dczia/theremini/documentation/gerber.png_Combined_Bottom.png

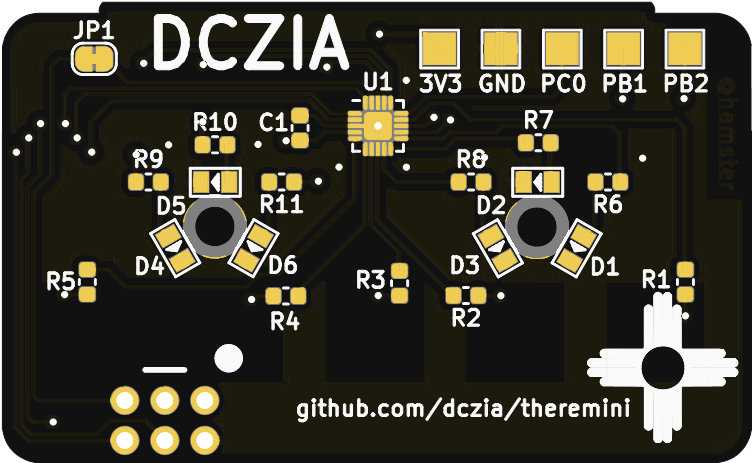
documentation/gerber.png_Combined_Bottom.png
