dczia/theremini/documentation/gerber.png_Combined_Top.png

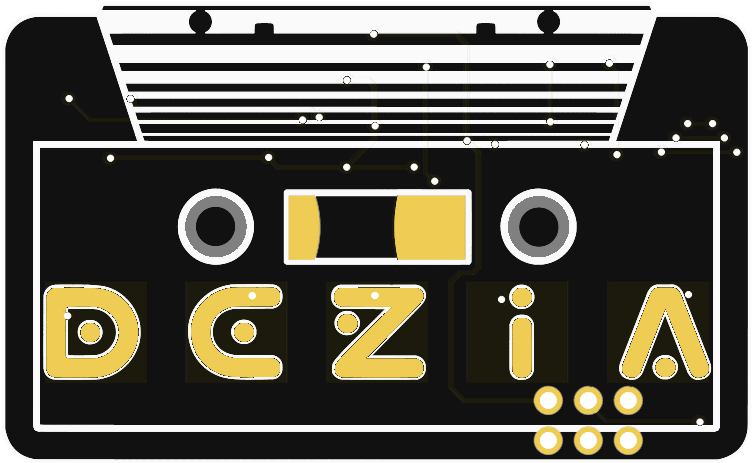
documentation/gerber.png_Combined_Top.png
