dczia/theremini/documentation/panel.png_Combined_Bottom.png

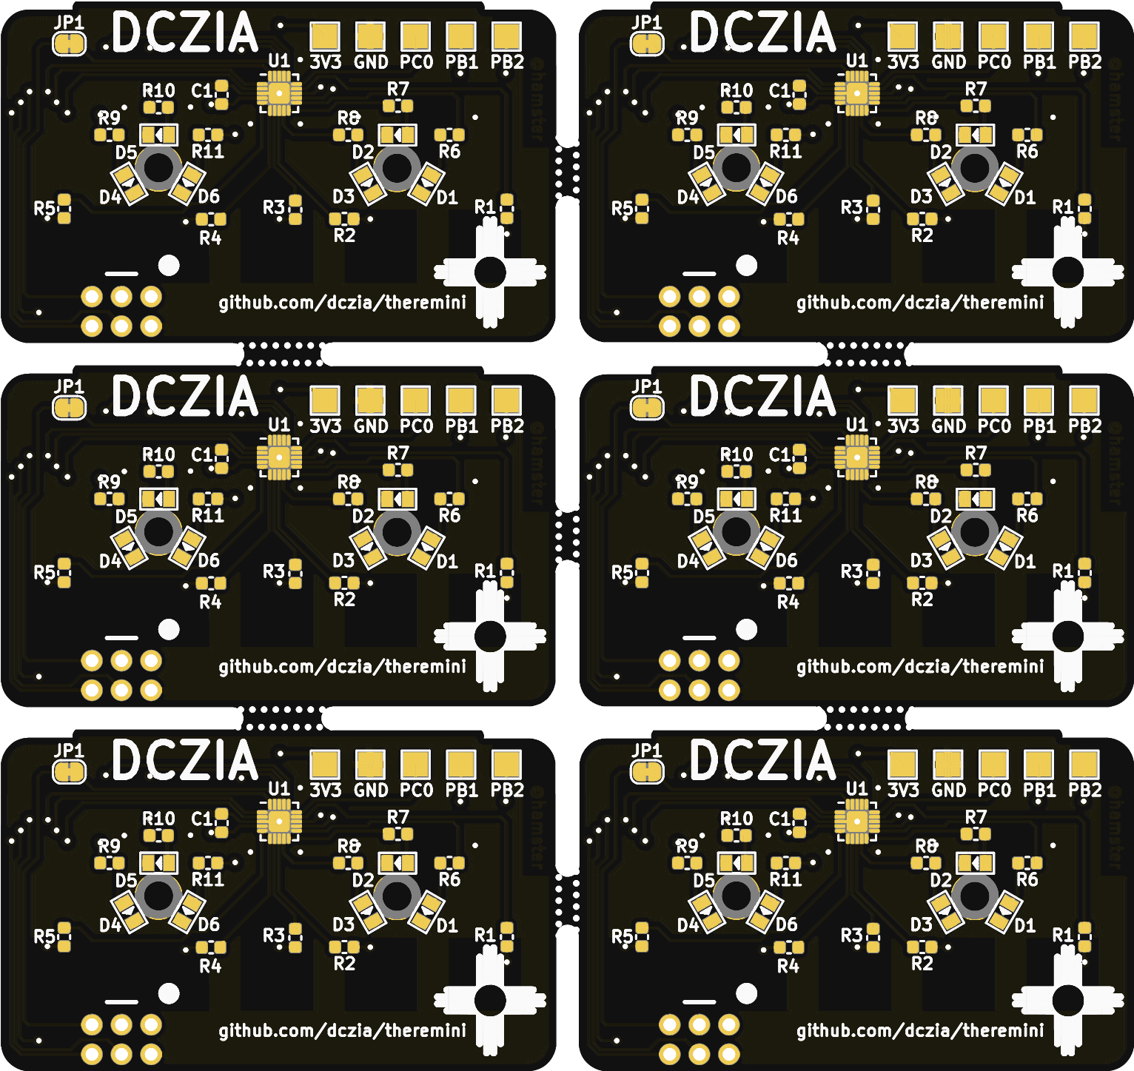
documentation/panel.png_Combined_Bottom.png
