dczia/theremini/documentation/panel.png_Combined_Top.png

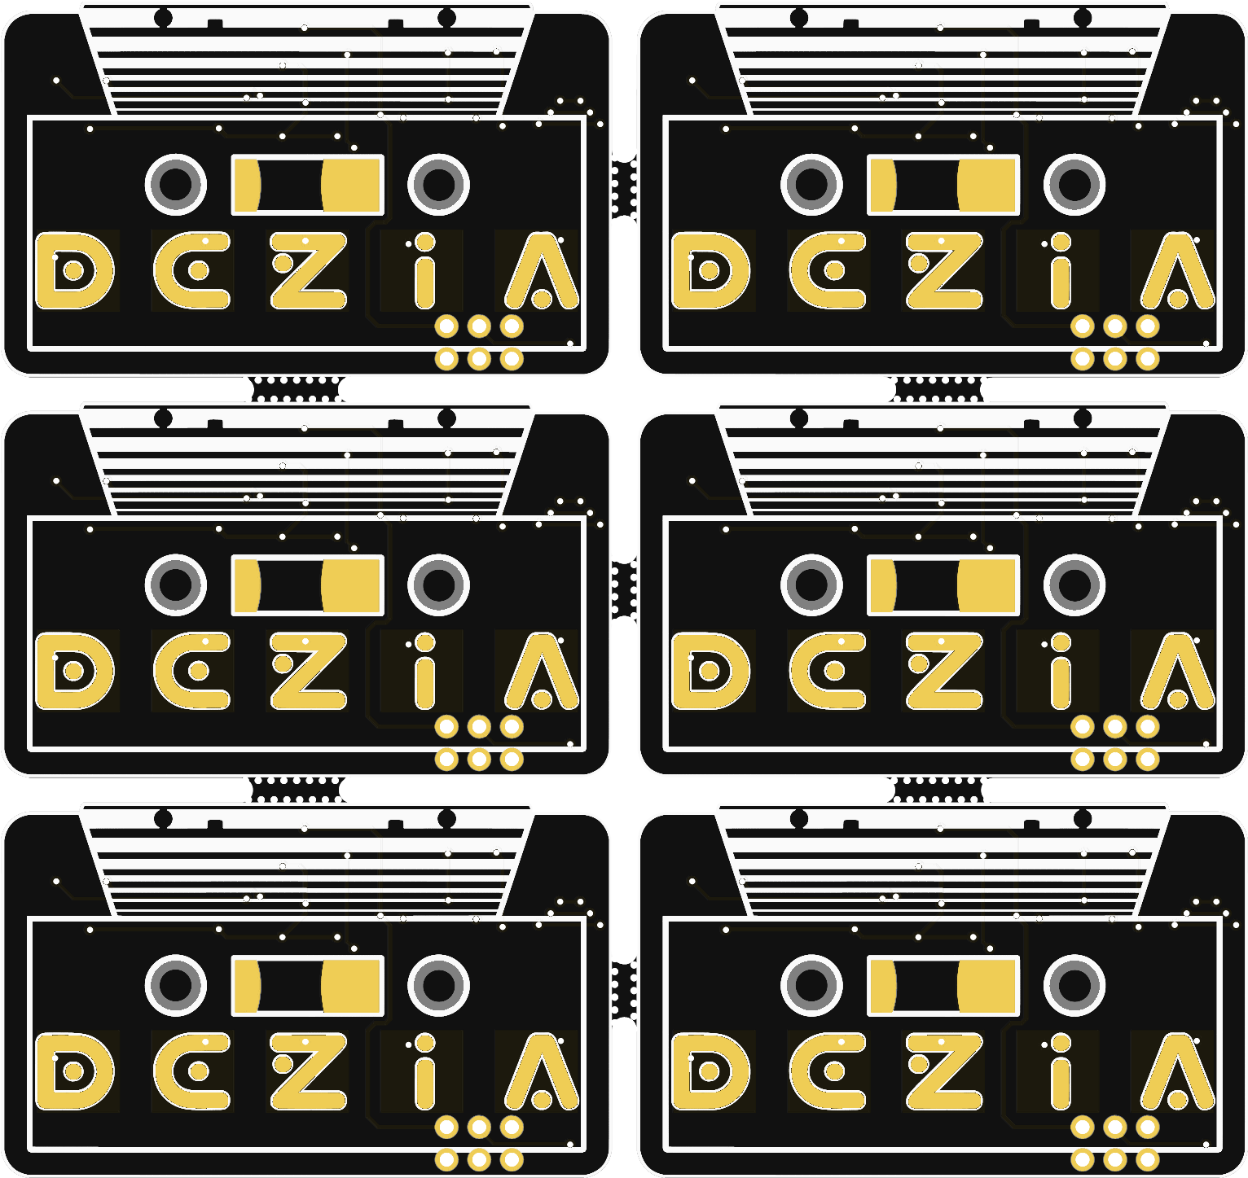
documentation/panel.png_Combined_Top.png
