dczia/theremini/gerber/panel/Panel_Combined_Bottom.png

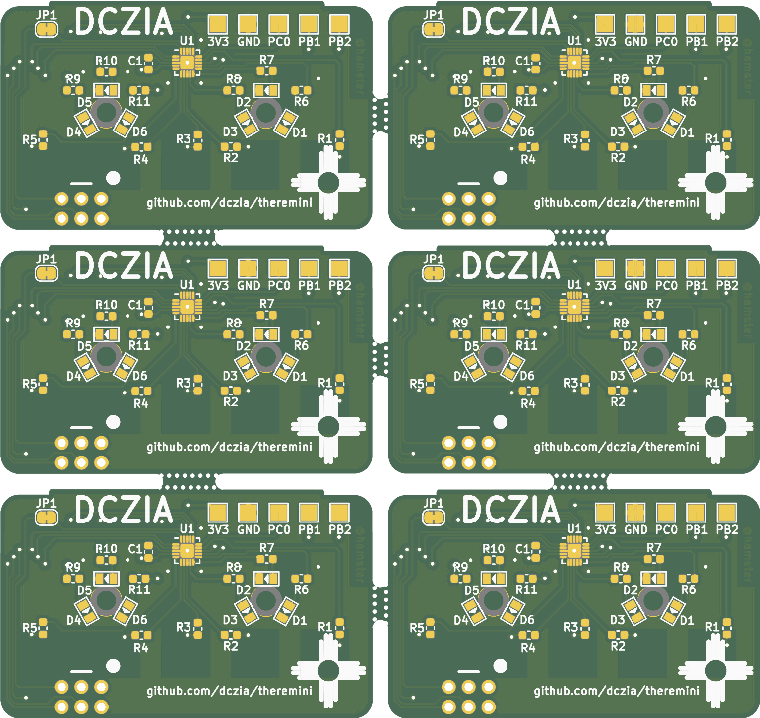
gerber/panel/Panel_Combined_Bottom.png
