dczia/theremini/images/laser-theremin-06.png

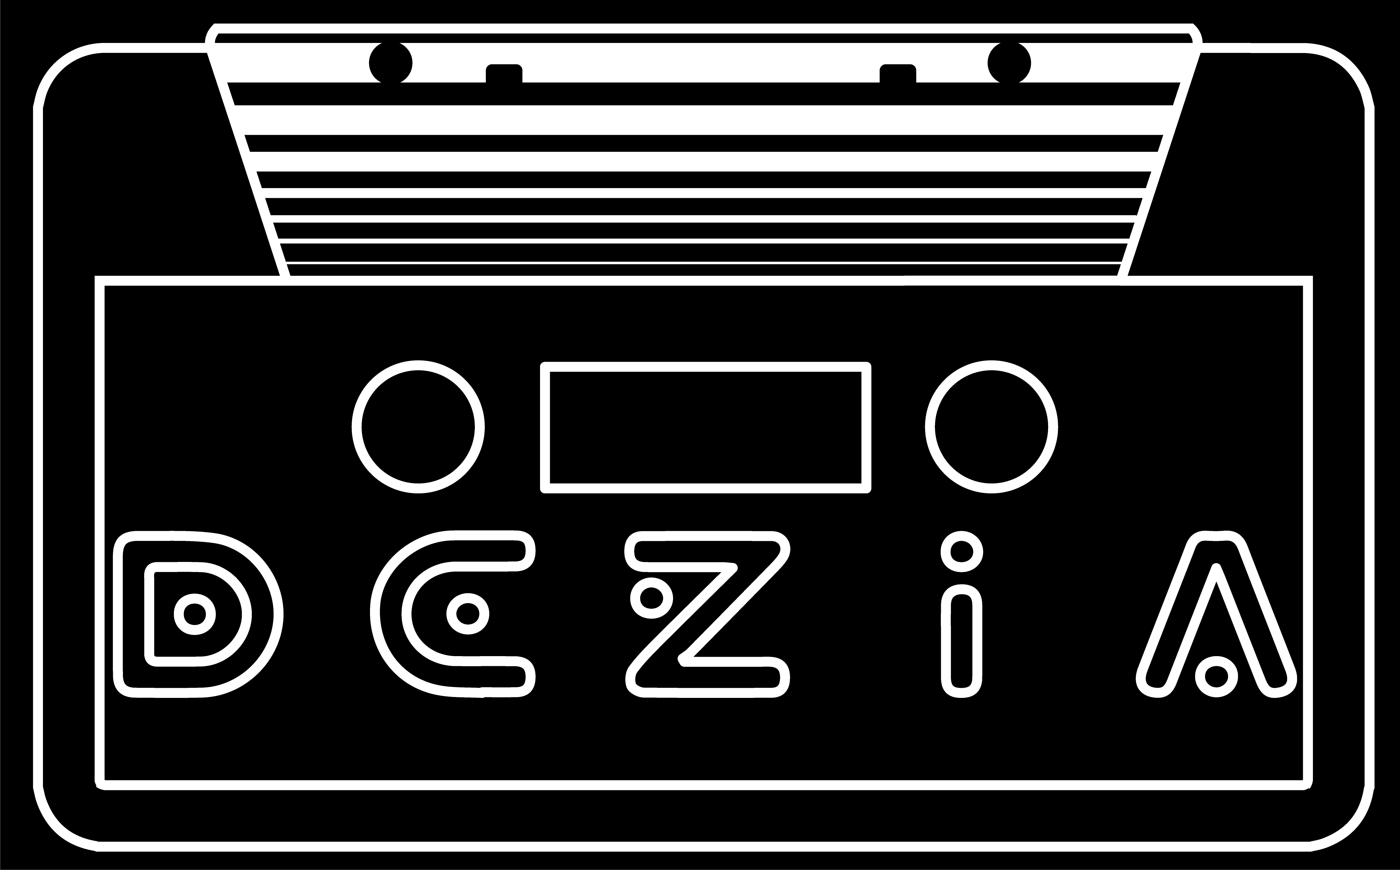
images/laser-theremin-06.png
